Luigimash/customMacropad/media/AUTOCAD1.png

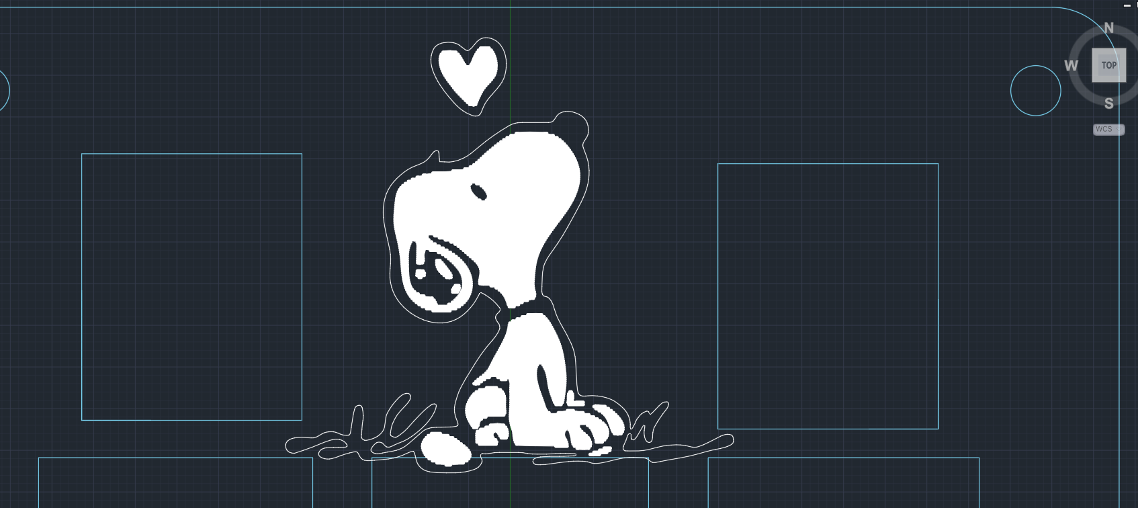
media/AUTOCAD1.png
