Luigimash/customMacropad/media/earlyAUTOCADMockup.png

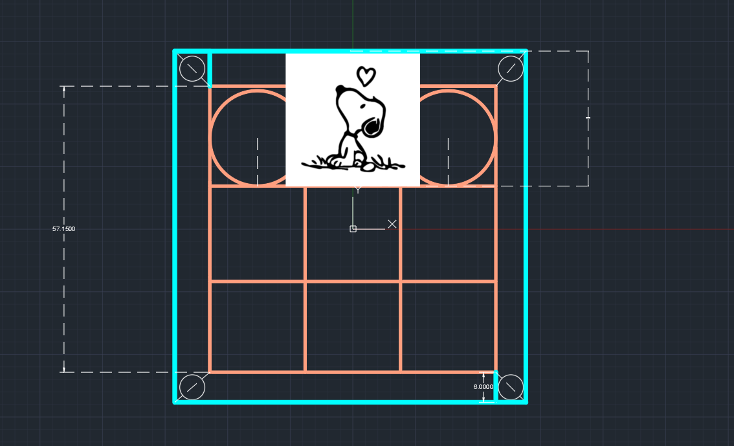
media/earlyAUTOCADMockup.png
