Luigimash/customMacropad/media/IMG_6349.jpg

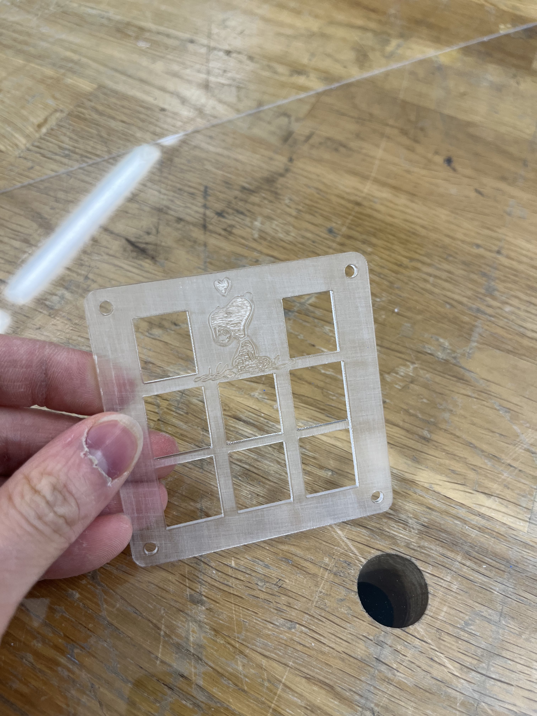
media/IMG_6349.jpg
