Luigimash/customMacropad/media/IMG_6408.jpg

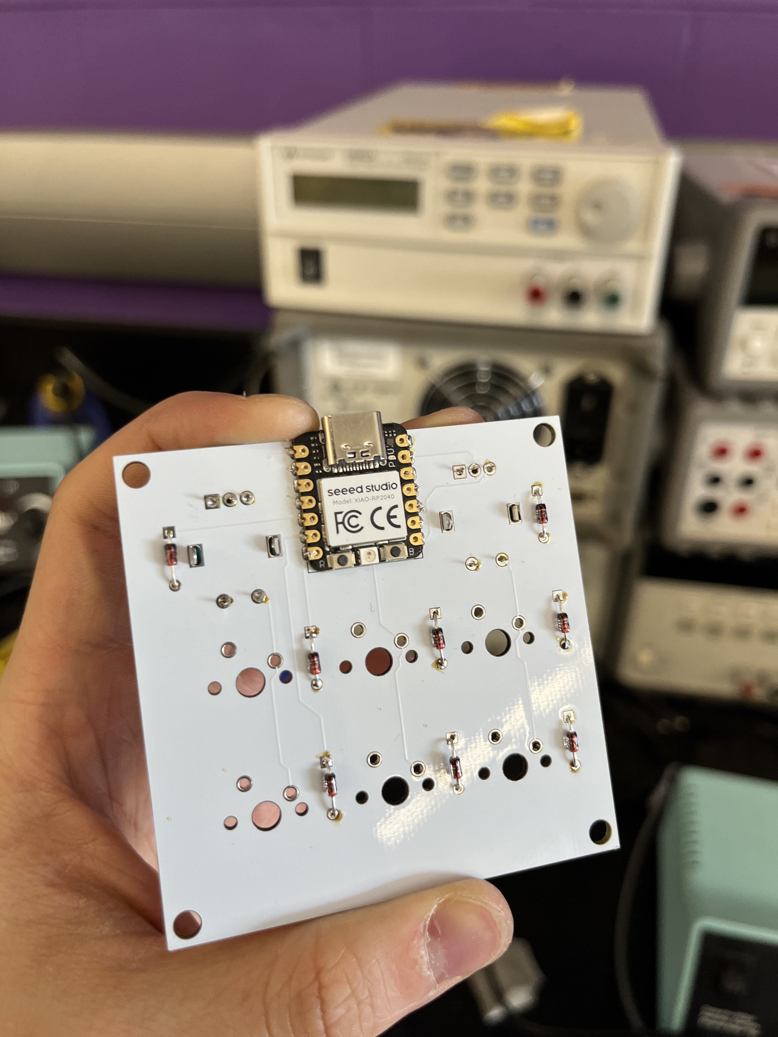
media/IMG_6408.jpg
