Luigimash/customMacropad/media/IMG_6409.jpg

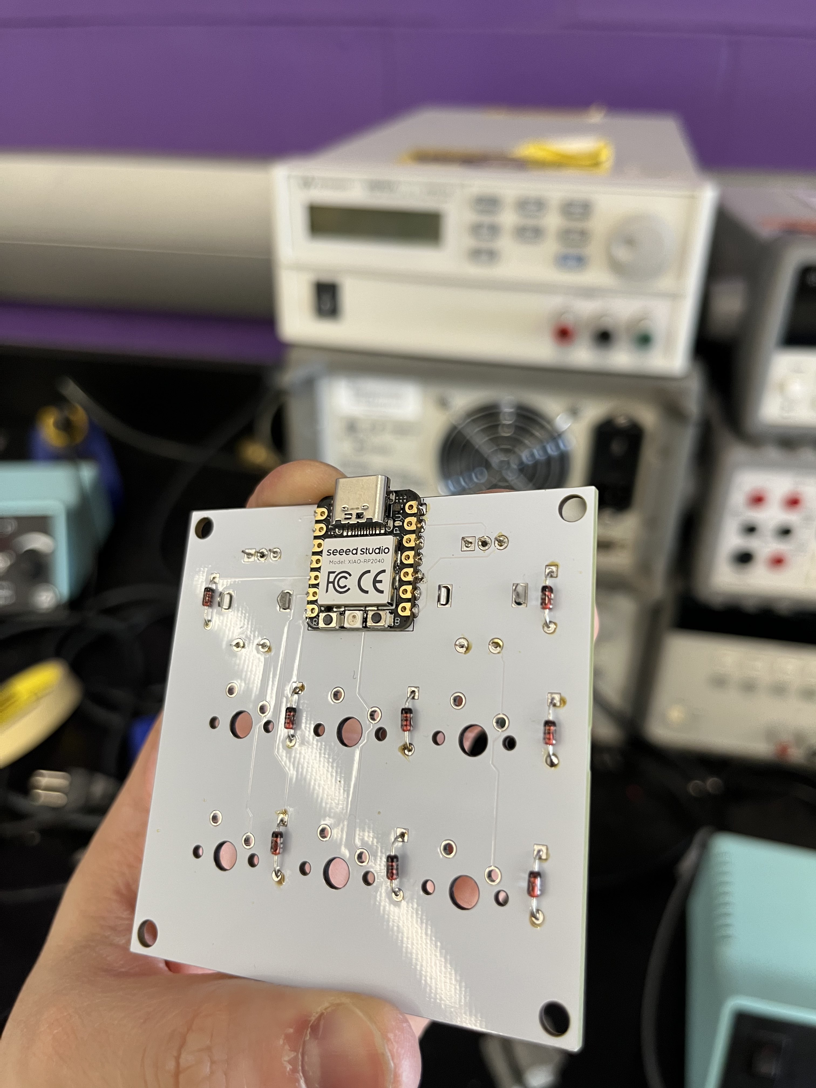
media/IMG_6409.jpg
