Luigimash/customMacropad/media/IMG_6410.jpg

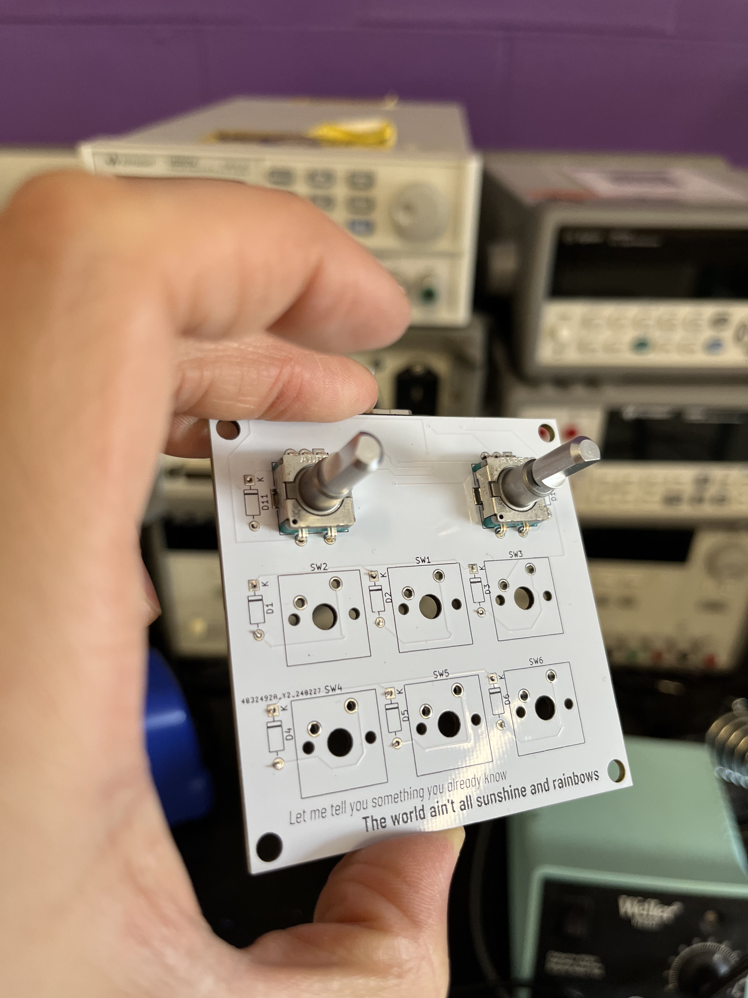
media/IMG_6410.jpg
