Luigimash/customMacropad/media/IMG_6450.jpg

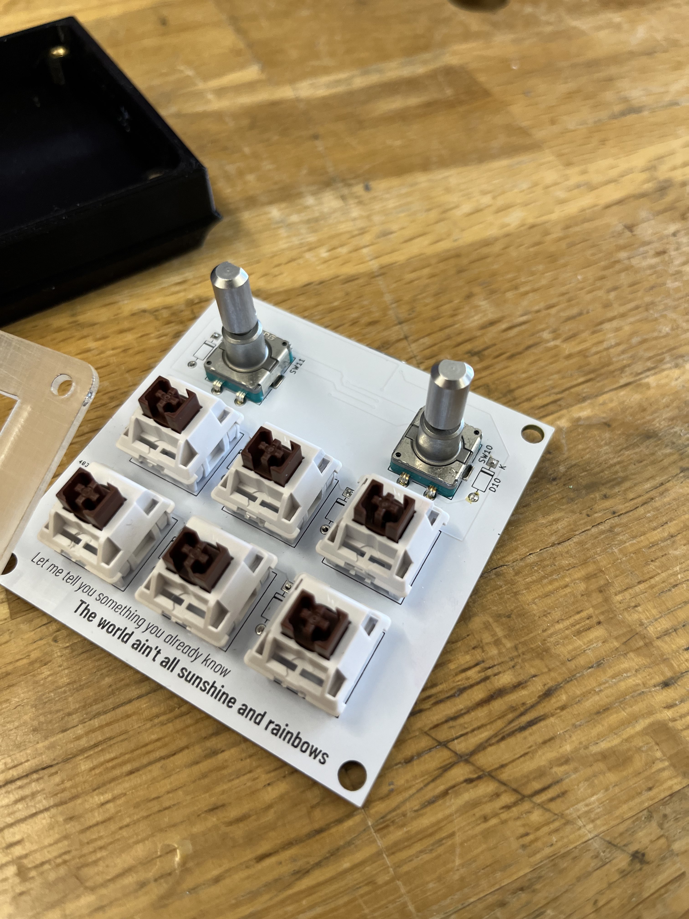
media/IMG_6450.jpg
