Luigimash/customMacropad/media/IMG_6451.jpg

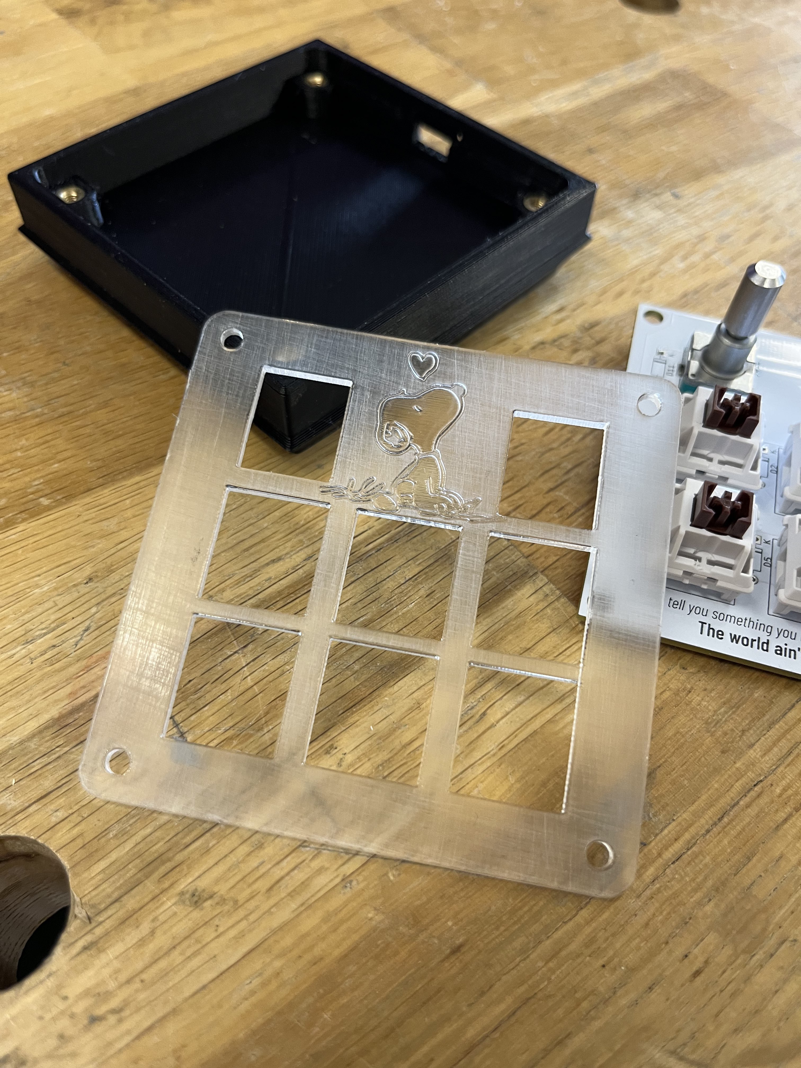
media/IMG_6451.jpg
