Luigimash/customMacropad/media/IMG_6452.jpg

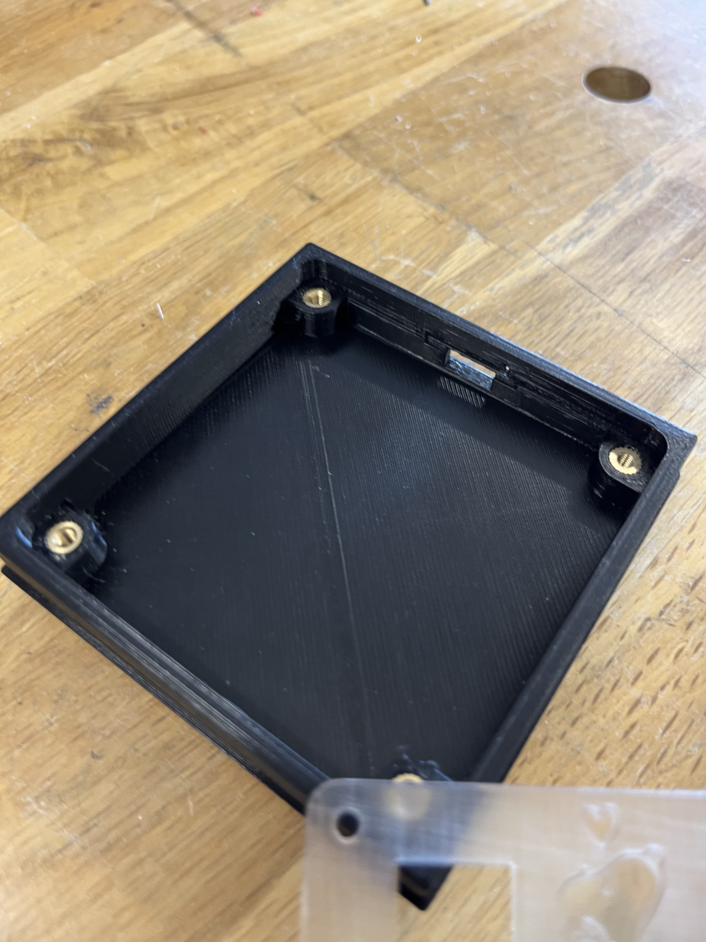
media/IMG_6452.jpg
