Luigimash/customMacropad/media/PCB_3D.png

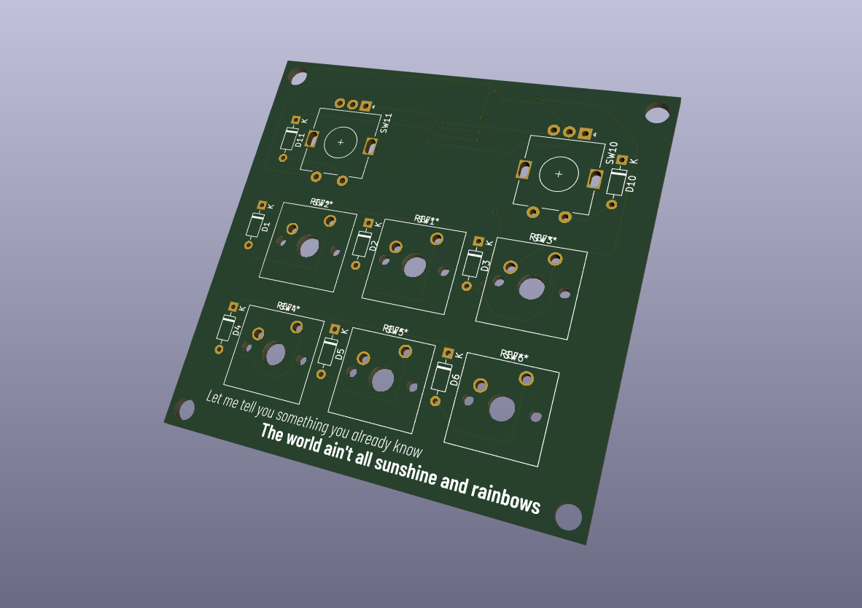
media/PCB_3D.png
